atoav/TH-VCO1/Board_Images/vco1-board-panel.jpg

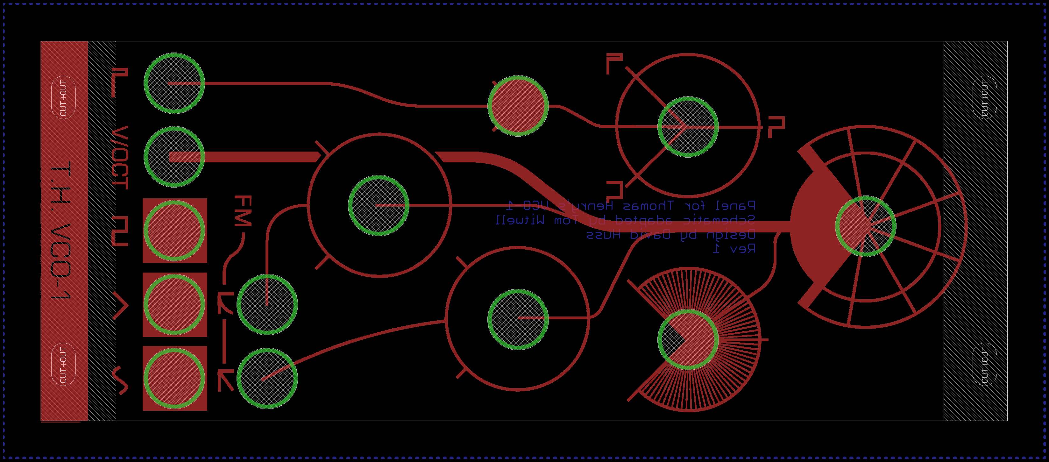
Board_Images/vco1-board-panel.jpg
