atoav/TH-VCO1/Board_Images/vco1-board-pots.jpg

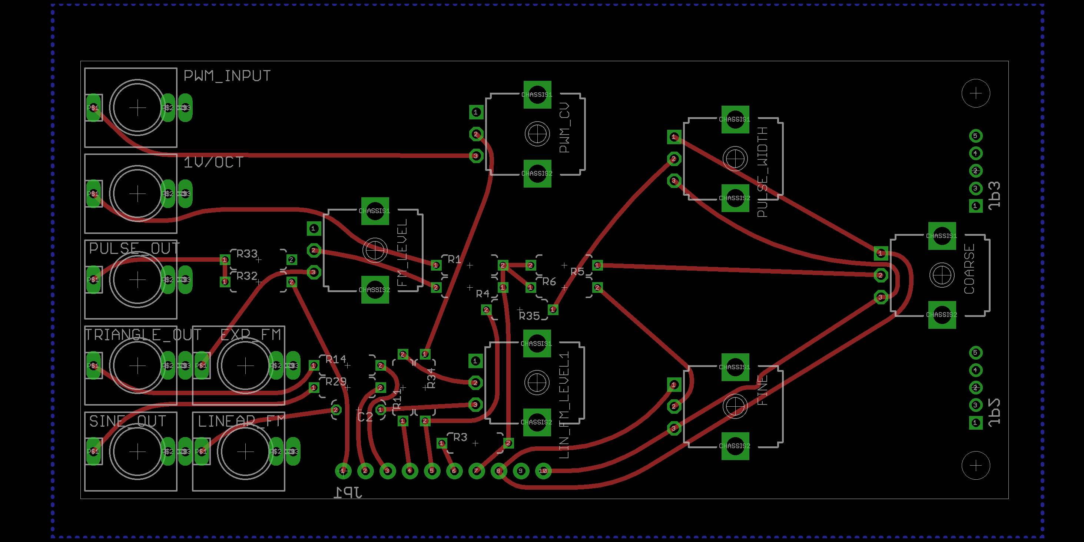
Board_Images/vco1-board-pots.jpg
